theinventorshouse/NodeMcu-v3-LiPoly-LiIon-Backpack/Model3DRevA.png

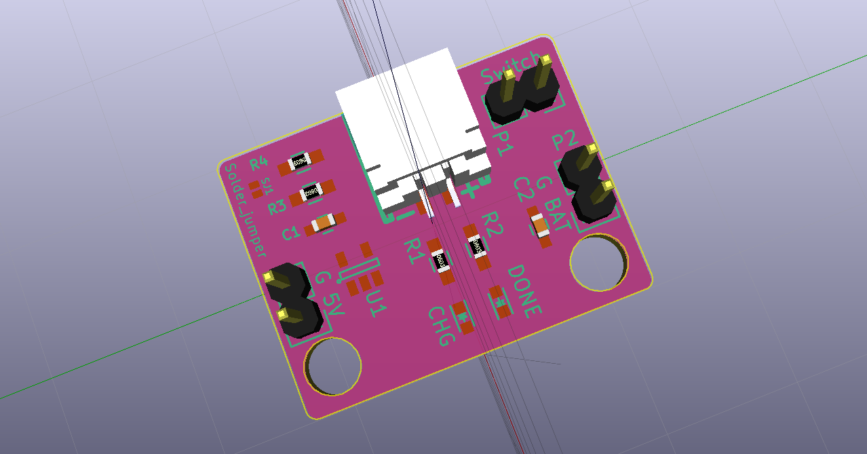
Model3DRevA.png
