theinventorshouse/NodeMcu-v3-LiPoly-LiIon-Backpack/Photos Rev.A Testing/IMG_20151228_190629810_HDR.jpg

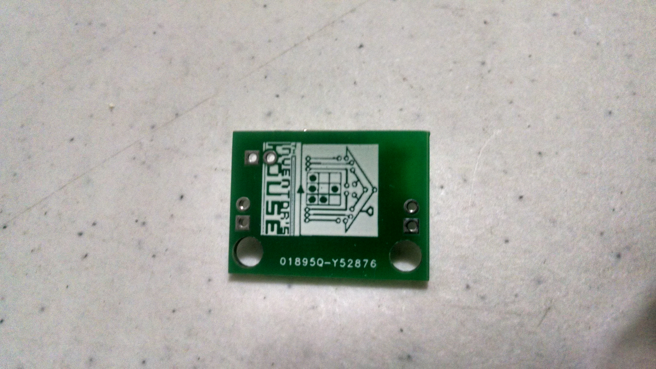
Photos Rev.A Testing/IMG_20151228_190629810_HDR.jpg
