theinventorshouse/NodeMcu-v3-LiPoly-LiIon-Backpack/Photos Rev.A Testing/IMG_20151229_145952536.jpg

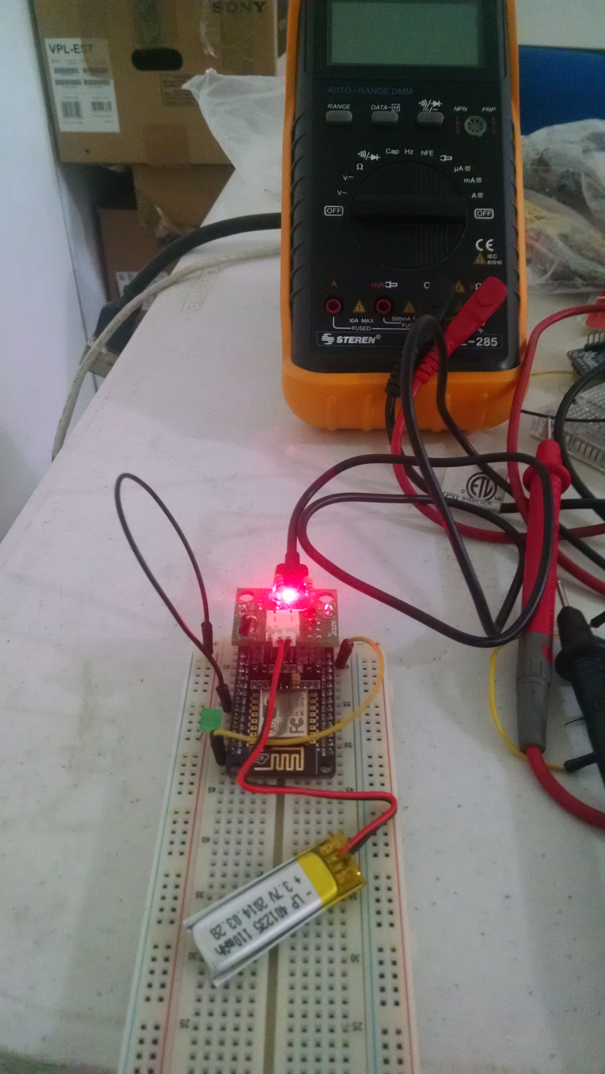
Photos Rev.A Testing/IMG_20151229_145952536.jpg
