theinventorshouse/NodeMcu-v3-LiPoly-LiIon-Backpack/Photos Rev.A Testing/IMG_20151229_145956588.jpg

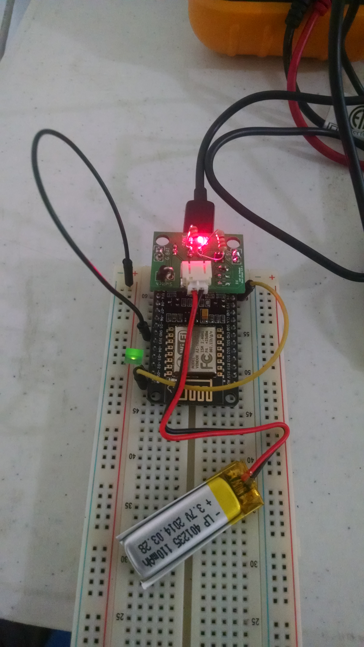
Photos Rev.A Testing/IMG_20151229_145956588.jpg
